wikihouseproject/Skylark/SKYLARK150/Openings/W-O-L-4/W-O-L-4_cnc/W-O-L-4-G.dxf

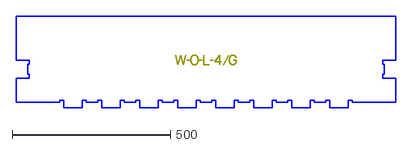
[picture p11: CAD file, 2026-10-01]
SKYLARK150/Openings/W-O-L-4/W-O-L-4_cnc/W-O-L-4-G.dxf
1199.5 x 289.5
