wikihouseproject/Skylark/SKYLARK150/Openings/W-O-L-5/W-O-L-5_cnc/W-O-L-5-B.dxf

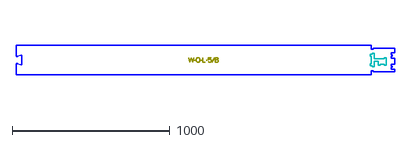
[picture p12: CAD file, 2026-10-01]
SKYLARK150/Openings/W-O-L-5/W-O-L-5_cnc/W-O-L-5-B.dxf
2399.5 x 185.5
