wikihouseproject/Skylark/SKYLARK150/Openings/W-O-M-1/W-O-M-1_cnc/W-O-M-1-I.dxf

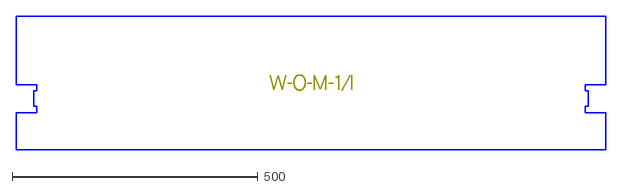
[picture p13: CAD file, 2026-10-01]
SKYLARK150/Openings/W-O-M-1/W-O-M-1_cnc/W-O-M-1-I.dxf
1199.5 x 271.5
