wikihouseproject/Skylark/SKYLARK150/Openings/W-O-M-2/W-O-M-2_cnc/W-O-M-2-B.dxf

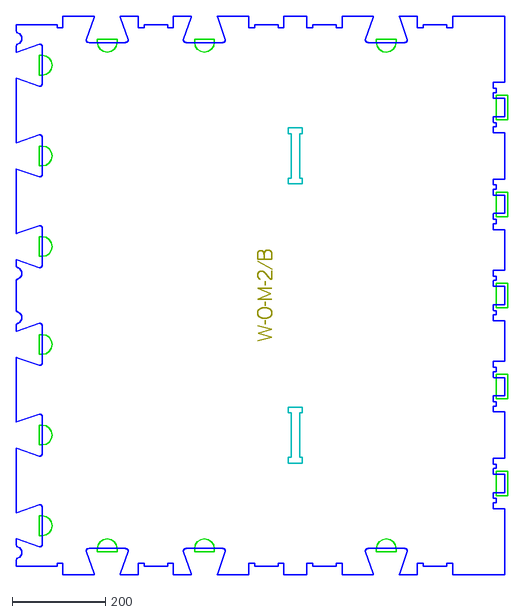
[picture p14: CAD file, 2026-10-01]
SKYLARK150/Openings/W-O-M-2/W-O-M-2_cnc/W-O-M-2-B.dxf
1056.0 x 1199.5
