wikihouseproject/Skylark/SKYLARK150/Openings/W-O-M-3/W-O-M-3_cnc/W-O-M-3-G.dxf

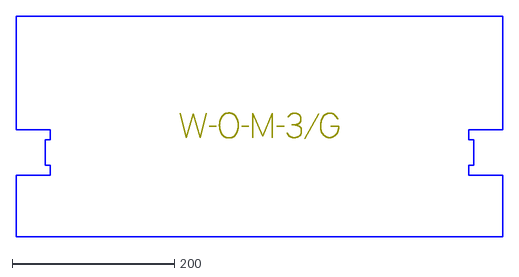
[picture p15: CAD file, 2026-10-01]
SKYLARK150/Openings/W-O-M-3/W-O-M-3_cnc/W-O-M-3-G.dxf
599.5 x 271.5
