wikihouseproject/Skylark/SKYLARK150/Openings/W-O-M-4/W-O-M-4_cnc/W-O-M-4-C.dxf

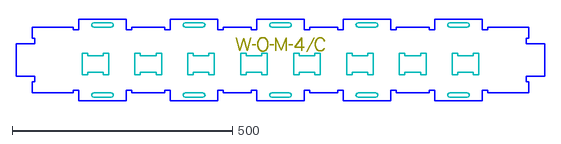
[picture p16: CAD file, 2026-10-01]
SKYLARK150/Openings/W-O-M-4/W-O-M-4_cnc/W-O-M-4-C.dxf
1199.5 x 185.6
