wikihouseproject/Skylark/SKYLARK150/Openings/W-O-M-5/W-O-M-5_cnc/W-O-M-5-C.dxf

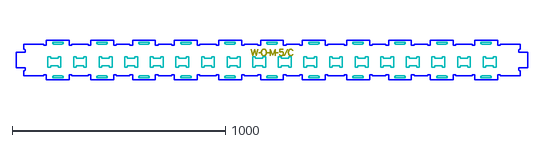
[picture p17: CAD file, 2026-10-01]
SKYLARK150/Openings/W-O-M-5/W-O-M-5_cnc/W-O-M-5-C.dxf
2399.5 x 185.6
