wikihouseproject/Skylark/SKYLARK150/Openings/W-O-S-1/W-O-S-1_cnc/W-O-S-1-H.dxf

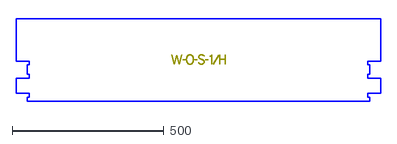
[picture p18: CAD file, 2026-10-01]
SKYLARK150/Openings/W-O-S-1/W-O-S-1_cnc/W-O-S-1-H.dxf
1199.5 x 271.5
