wikihouseproject/Skylark/SKYLARK150/Openings/W-O-S-2/W-O-S-2_cnc/W-O-S-2-B.dxf

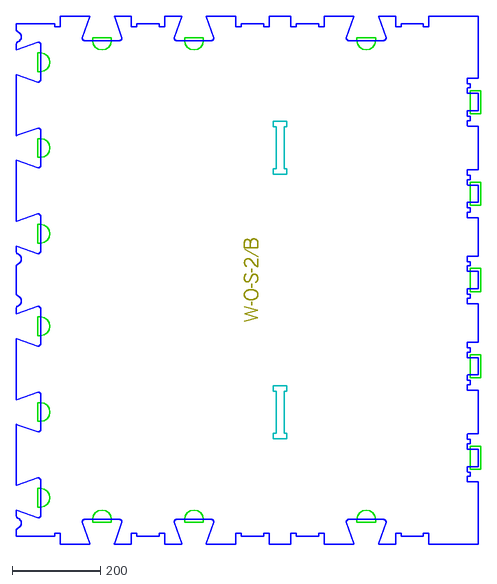
[picture p19: CAD file, 2026-10-01]
SKYLARK150/Openings/W-O-S-2/W-O-S-2_cnc/W-O-S-2-B.dxf
1056.0 x 1199.5
