wikihouseproject/Skylark/SKYLARK150/Openings/W-O-S-3/W-O-S-3_cnc/W-O-S-3-A.dxf

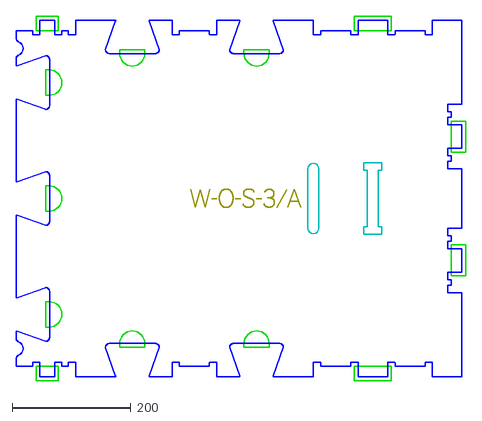
[picture p20: CAD file, 2026-10-01]
SKYLARK150/Openings/W-O-S-3/W-O-S-3_cnc/W-O-S-3-A.dxf
756.0 x 612.5
