wikihouseproject/Skylark/SKYLARK150/Openings/W-O-S-4/W-O-S-4_cnc/W-O-S-4-C.dxf

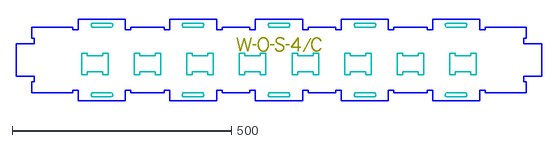
[picture p21: CAD file, 2026-10-01]
SKYLARK150/Openings/W-O-S-4/W-O-S-4_cnc/W-O-S-4-C.dxf
1199.5 x 185.6
