wikihouseproject/Skylark/SKYLARK150/Openings/W-O-S-5/W-O-S-5_cnc/W-O-S-5-A.dxf

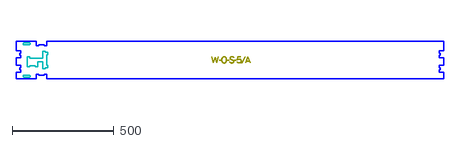
[picture p22: CAD file, 2026-10-01]
SKYLARK150/Openings/W-O-S-5/W-O-S-5_cnc/W-O-S-5-A.dxf
2099.5 x 185.5
