wikihouseproject/Skylark/SKYLARK150/Roofs/R-L-42/R-L-42_cnc/R-L-42-J.dxf

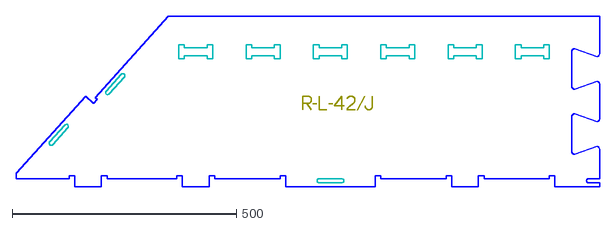
[picture p23: CAD file, 2026-10-01]
SKYLARK150/Roofs/R-L-42/R-L-42_cnc/R-L-42-J.dxf
1299.5 x 379.5
