wikihouseproject/Skylark/SKYLARK150/Roofs/R-L/R-L_cnc/R-L-A.dxf

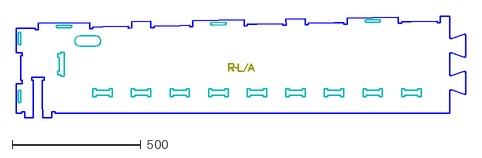
[picture p24: CAD file, 2026-10-01]
SKYLARK150/Roofs/R-L/R-L_cnc/R-L-A.dxf
1747.5 x 394.6
