wikihouseproject/Skylark/SKYLARK150/Roofs/R-S-42/R-S-42_cnc/R-S-42-A.dxf

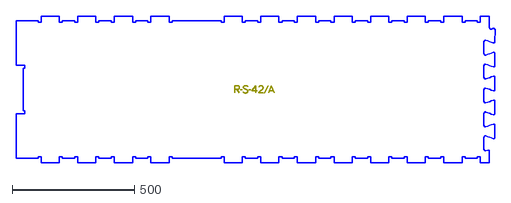
[picture p25: CAD file, 2026-10-01]
SKYLARK150/Roofs/R-S-42/R-S-42_cnc/R-S-42-A.dxf
1962.6 x 599.5
