wikihouseproject/Skylark/SKYLARK150/Roofs/R-S/R-S_cnc/R-S-L.dxf

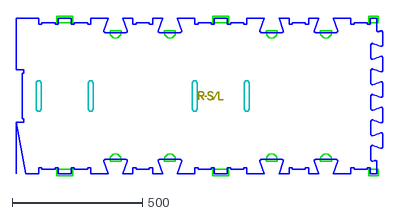
[picture p26: CAD file, 2026-10-01]
SKYLARK150/Roofs/R-S/R-S_cnc/R-S-L.dxf
1408.5 x 612.5
