wikihouseproject/Skylark/SKYLARK150/Roofs/R-XXS-42/R-XXS-42_cnc/R-XXS-42-A.dxf

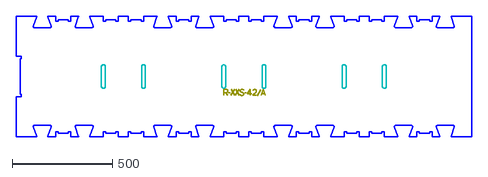
[picture p27: CAD file, 2026-10-01]
SKYLARK150/Roofs/R-XXS-42/R-XXS-42_cnc/R-XXS-42-A.dxf
2268.2 x 599.5
