wikihouseproject/Skylark/SKYLARK150/Roofs/R-XXS/R-XXS_cnc/R-XXS-J.dxf

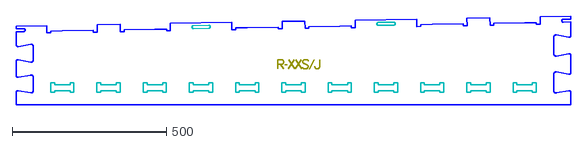
[picture p28: CAD file, 2026-10-01]
SKYLARK150/Roofs/R-XXS/R-XXS_cnc/R-XXS-J.dxf
1799.5 x 286.0
