wikihouseproject/Skylark/SKYLARK150/Walls/C-L-1/C-L-1_cnc/C-L-1-H.dxf

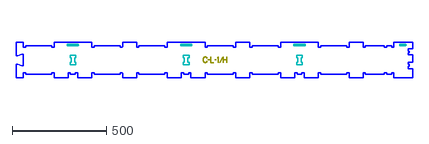
[picture p29: CAD file, 2026-10-01]
SKYLARK150/Walls/C-L-1/C-L-1_cnc/C-L-1-H.dxf
2099.5 x 185.5
