wikihouseproject/Skylark/SKYLARK150/Walls/C-L-2/C-L-2_cnc/C-L-2-E.dxf

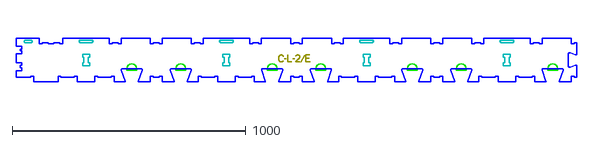
[picture p30: CAD file, 2026-10-01]
SKYLARK150/Walls/C-L-2/C-L-2_cnc/C-L-2-E.dxf
2399.5 x 185.5
