wikihouseproject/Skylark/SKYLARK150/Walls/C-M-1/C-M-1_cnc/C-M-1-C.dxf

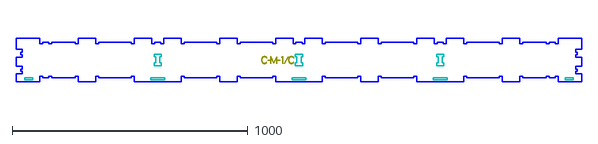
[picture p31: CAD file, 2026-10-01]
SKYLARK150/Walls/C-M-1/C-M-1_cnc/C-M-1-C.dxf
2399.5 x 185.5
