wikihouseproject/Skylark/SKYLARK150/Walls/C-M-2/C-M-2_cnc/C-M-2-E.dxf

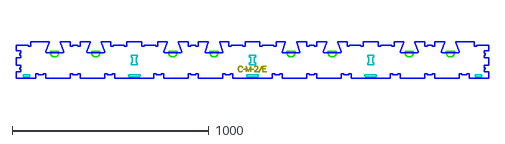
[picture p32: CAD file, 2026-10-01]
SKYLARK150/Walls/C-M-2/C-M-2_cnc/C-M-2-E.dxf
2399.5 x 185.5
