wikihouseproject/Skylark/SKYLARK150/Walls/C-S-1/C-S-1_cnc/C-S-1-B.dxf

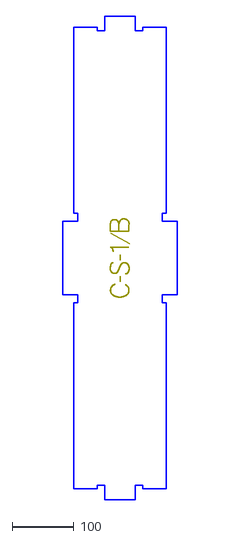
[picture p33: CAD file, 2026-10-01]
SKYLARK150/Walls/C-S-1/C-S-1_cnc/C-S-1-B.dxf
185.5 x 785.5
