wikihouseproject/Skylark/SKYLARK150/Walls/C-S-2/C-S-2_cnc/C-S-2-D.dxf

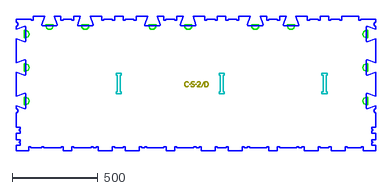
[picture p34: CAD file, 2026-10-01]
SKYLARK150/Walls/C-S-2/C-S-2_cnc/C-S-2-D.dxf
2099.5 x 785.5
