wikihouseproject/Skylark/SKYLARK150/Walls/G-S-42-1/G-S-42-1_cnc/G-S-42-1-A.dxf

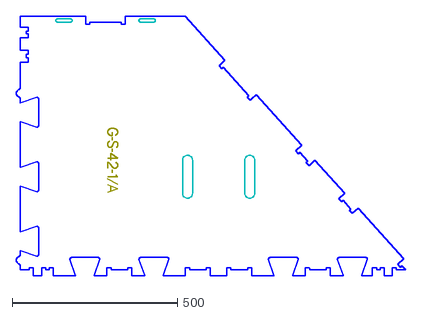
[picture p35: CAD file, 2026-10-01]
SKYLARK150/Walls/G-S-42-1/G-S-42-1_cnc/G-S-42-1-A.dxf
1177.3 x 785.5
