wikihouseproject/Skylark/SKYLARK150/Walls/G-S-42-2/G-S-42-2_cnc/G-S-42-2-E.dxf

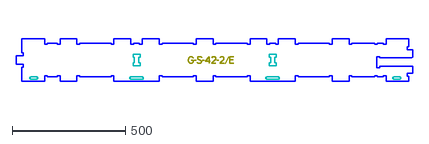
[picture p36: CAD file, 2026-10-01]
SKYLARK150/Walls/G-S-42-2/G-S-42-2_cnc/G-S-42-2-E.dxf
1748.2 x 185.5
