wikihouseproject/Skylark/SKYLARK150/Walls/G-S-42-3/G-S-42-3_cnc/G-S-42-3-E.dxf

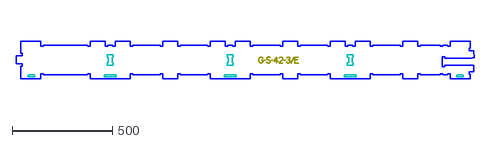
[picture p37: CAD file, 2026-10-01]
SKYLARK150/Walls/G-S-42-3/G-S-42-3_cnc/G-S-42-3-E.dxf
2288.4 x 185.5
