wikihouseproject/Skylark/SKYLARK150/Walls/G-S-42-4/G-S-42-4_cnc/G-S-42-4-A.dxf

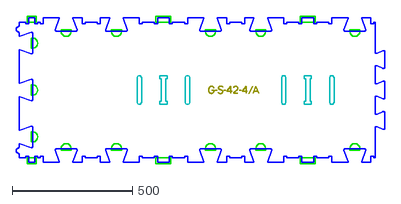
[picture p38: CAD file, 2026-10-01]
SKYLARK150/Walls/G-S-42-4/G-S-42-4_cnc/G-S-42-4-A.dxf
1531.5 x 612.5
