wikihouseproject/Skylark/SKYLARK150/Walls/G-S-42-4R/G-S-42-4R_cnc/G-S-42-4R-C.dxf

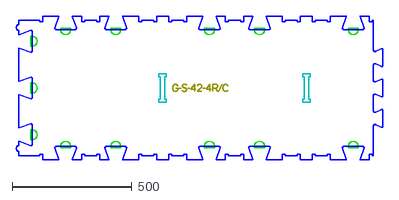
[picture p39: CAD file, 2026-10-01]
SKYLARK150/Walls/G-S-42-4R/G-S-42-4R_cnc/G-S-42-4R-C.dxf
1531.5 x 599.5
