wikihouseproject/Skylark/SKYLARK150/Walls/G-S-42-5R/G-S-42-5R_cnc/G-S-42-5R-C.dxf

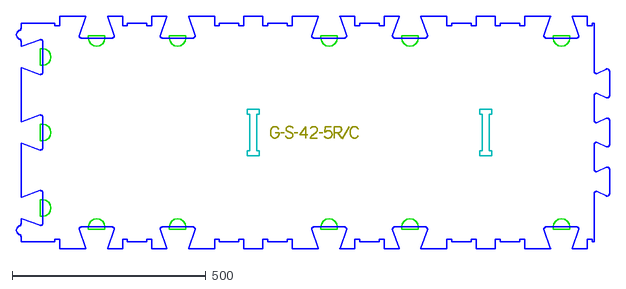
[picture p40: CAD file, 2026-10-01]
SKYLARK150/Walls/G-S-42-5R/G-S-42-5R_cnc/G-S-42-5R-C.dxf
1531.5 x 599.5
