wikihouseproject/Skylark/SKYLARK150/Walls/G-S-42-6/G-S-42-6_cnc/G-S-42-6-C.dxf

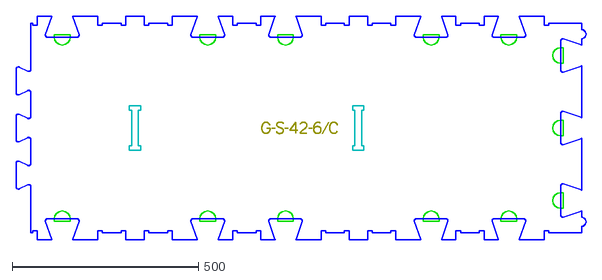
[picture p41: CAD file, 2026-10-01]
SKYLARK150/Walls/G-S-42-6/G-S-42-6_cnc/G-S-42-6-C.dxf
1531.5 x 599.5
