wikihouseproject/Skylark/SKYLARK150/Walls/G-S-42-7/G-S-42-7_cnc/G-S-42-7-C.dxf

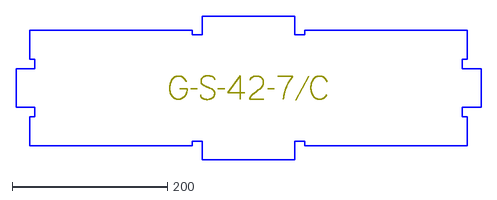
[picture p42: CAD file, 2026-10-01]
SKYLARK150/Walls/G-S-42-7/G-S-42-7_cnc/G-S-42-7-C.dxf
599.5 x 185.5
