wikihouseproject/Skylark/SKYLARK150/Walls/G-S-42-8/G-S-42-8_cnc/G-S-42-8-D.dxf

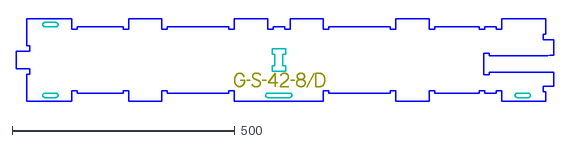
[picture p43: CAD file, 2026-10-01]
SKYLARK150/Walls/G-S-42-8/G-S-42-8_cnc/G-S-42-8-D.dxf
1207.9 x 185.5
