wikihouseproject/Skylark/SKYLARK150/Walls/G-S-42-9/G-S-42-9_cnc/G-S-42-9-E.dxf

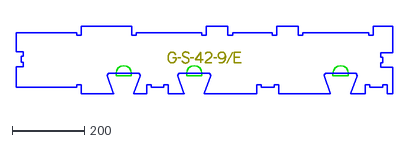
[picture p44: CAD file, 2026-10-01]
SKYLARK150/Walls/G-S-42-9/G-S-42-9_cnc/G-S-42-9-E.dxf
1042.2 x 185.5
