wikihouseproject/Skylark/SKYLARK150/Walls/G-XXS-42-1/G-XXS-42-1_cnc/G-XXS-42-1-E.dxf

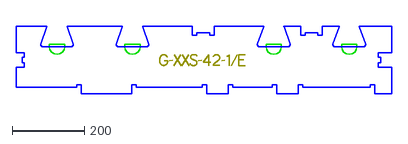
[picture p45: CAD file, 2026-10-01]
SKYLARK150/Walls/G-XXS-42-1/G-XXS-42-1_cnc/G-XXS-42-1-E.dxf
1039.1 x 185.5
