wikihouseproject/Skylark/SKYLARK150/Walls/G-XXS-42-2/G-XXS-42-2_cnc/G-XXS-42-2-F.dxf

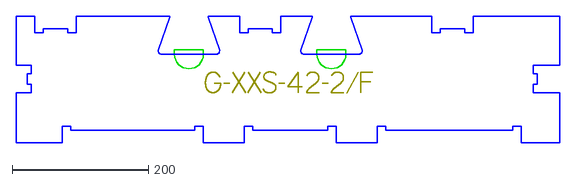
[picture p46: CAD file, 2026-10-01]
SKYLARK150/Walls/G-XXS-42-2/G-XXS-42-2_cnc/G-XXS-42-2-F.dxf
796.5 x 185.5
