wikihouseproject/Skylark/SKYLARK150/Walls/G-XXS-42-3R/G-XXS-42-3R_cnc/G-XXS-42-3R-E.dxf

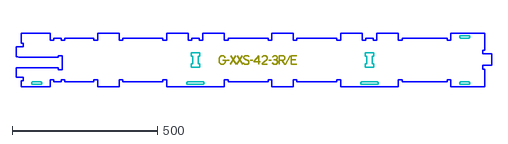
[picture p47: CAD file, 2026-10-01]
SKYLARK150/Walls/G-XXS-42-3R/G-XXS-42-3R_cnc/G-XXS-42-3R-E.dxf
1639.2 x 185.5
