wikihouseproject/Skylark/SKYLARK150/Walls/G-XXS-42-4/G-XXS-42-4_cnc/G-XXS-42-4-D.dxf

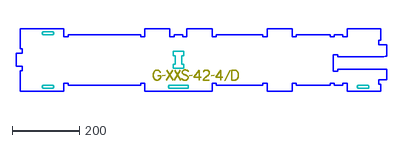
[picture p48: CAD file, 2026-10-01]
SKYLARK150/Walls/G-XXS-42-4/G-XXS-42-4_cnc/G-XXS-42-4-D.dxf
1098.8 x 185.5
