wikihouseproject/Skylark/SKYLARK150/Walls/G-XXS-42-5/G-XXS-42-5_cnc/G-XXS-42-5-B.dxf

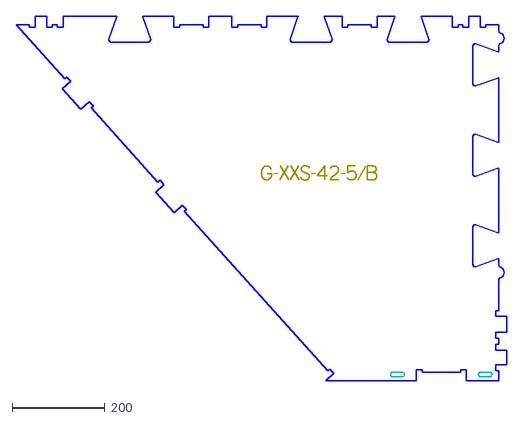
[picture p49: CAD file, 2026-10-01]
SKYLARK150/Walls/G-XXS-42-5/G-XXS-42-5_cnc/G-XXS-42-5-B.dxf
1058.3 x 785.6
