wikihouseproject/Skylark/SKYLARK150/Walls/V-L-1/V-L-1_cnc/V-L-1-K.dxf

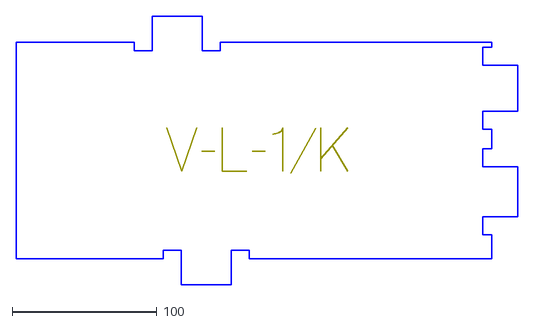
[picture p50: CAD file, 2026-10-01]
SKYLARK150/Walls/V-L-1/V-L-1_cnc/V-L-1-K.dxf
346.3 x 185.5
