wikihouseproject/Skylark/SKYLARK150/Walls/V-L-2/V-L-2_cnc/V-L-2-H.dxf

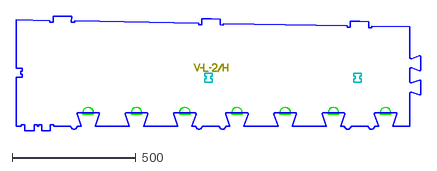
[picture p51: CAD file, 2026-10-01]
SKYLARK150/Walls/V-L-2/V-L-2_cnc/V-L-2-H.dxf
1633.4 x 463.0
