wikihouseproject/Skylark/SKYLARK150/Walls/V-S-1/V-S-1_cnc/V-S-1-A.dxf

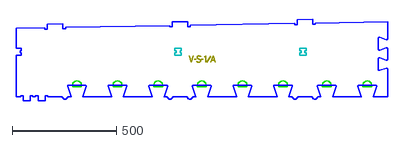
[picture p52: CAD file, 2026-10-01]
SKYLARK150/Walls/V-S-1/V-S-1_cnc/V-S-1-A.dxf
1782.9 x 389.7
