wikihouseproject/Skylark/SKYLARK150/Walls/V-S-2/V-S-2_cnc/V-S-2-J.dxf

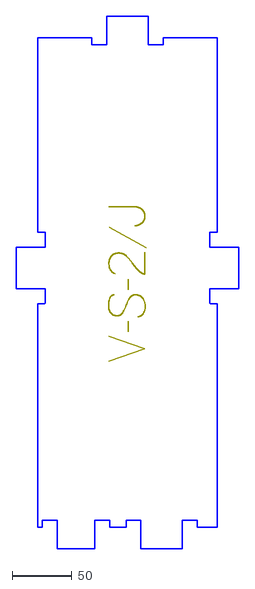
[picture p53: CAD file, 2026-10-01]
SKYLARK150/Walls/V-S-2/V-S-2_cnc/V-S-2-J.dxf
185.5 x 445.0
