wikihouseproject/Skylark/SKYLARK150/Walls/V-XXS-1/V-XXS-1_cnc/V-XXS-1-F.dxf

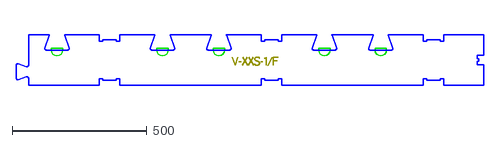
[picture p54: CAD file, 2026-10-01]
SKYLARK150/Walls/V-XXS-1/V-XXS-1_cnc/V-XXS-1-F.dxf
1731.4 x 185.5
