wikihouseproject/Skylark/SKYLARK150/Walls/V-XXS-2/V-XXS-2_cnc/V-XXS-2-E.dxf

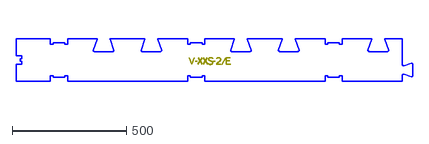
[picture p55: CAD file, 2026-10-01]
SKYLARK150/Walls/V-XXS-2/V-XXS-2_cnc/V-XXS-2-E.dxf
1731.4 x 185.5
