wikihouseproject/Skylark/SKYLARK150/Walls/W-L/W-L_cnc/W-L-B.dxf

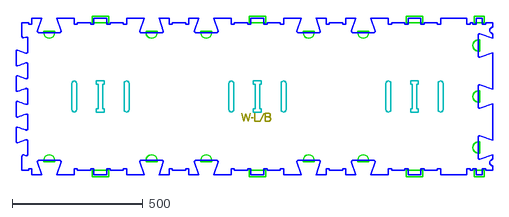
[picture p56: CAD file, 2026-10-01]
SKYLARK150/Walls/W-L/W-L_cnc/W-L-B.dxf
1822.1 x 612.5
