wikihouseproject/Skylark/SKYLARK150/Walls/W-M/W-M_cnc/W-M-C.dxf

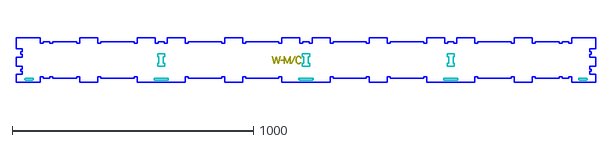
[picture p57: CAD file, 2026-10-01]
SKYLARK150/Walls/W-M/W-M_cnc/W-M-C.dxf
2399.5 x 185.5
