wikihouseproject/Skylark/SKYLARK150/Walls/W-S/W-S_cnc/W-S-A.dxf

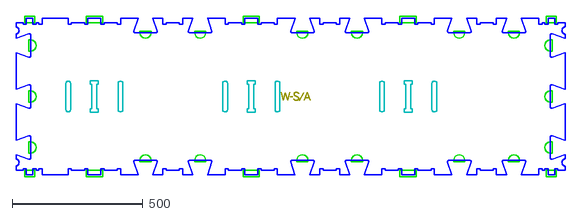
[picture p58: CAD file, 2026-10-01]
SKYLARK150/Walls/W-S/W-S_cnc/W-S-A.dxf
2099.5 x 612.5
