wikihouseproject/Skylark/SKYLARK200/Other/SKYLARK200_COMB-F_END-Y2/SKYLARK200_COMB-F_END-Y1.dxf

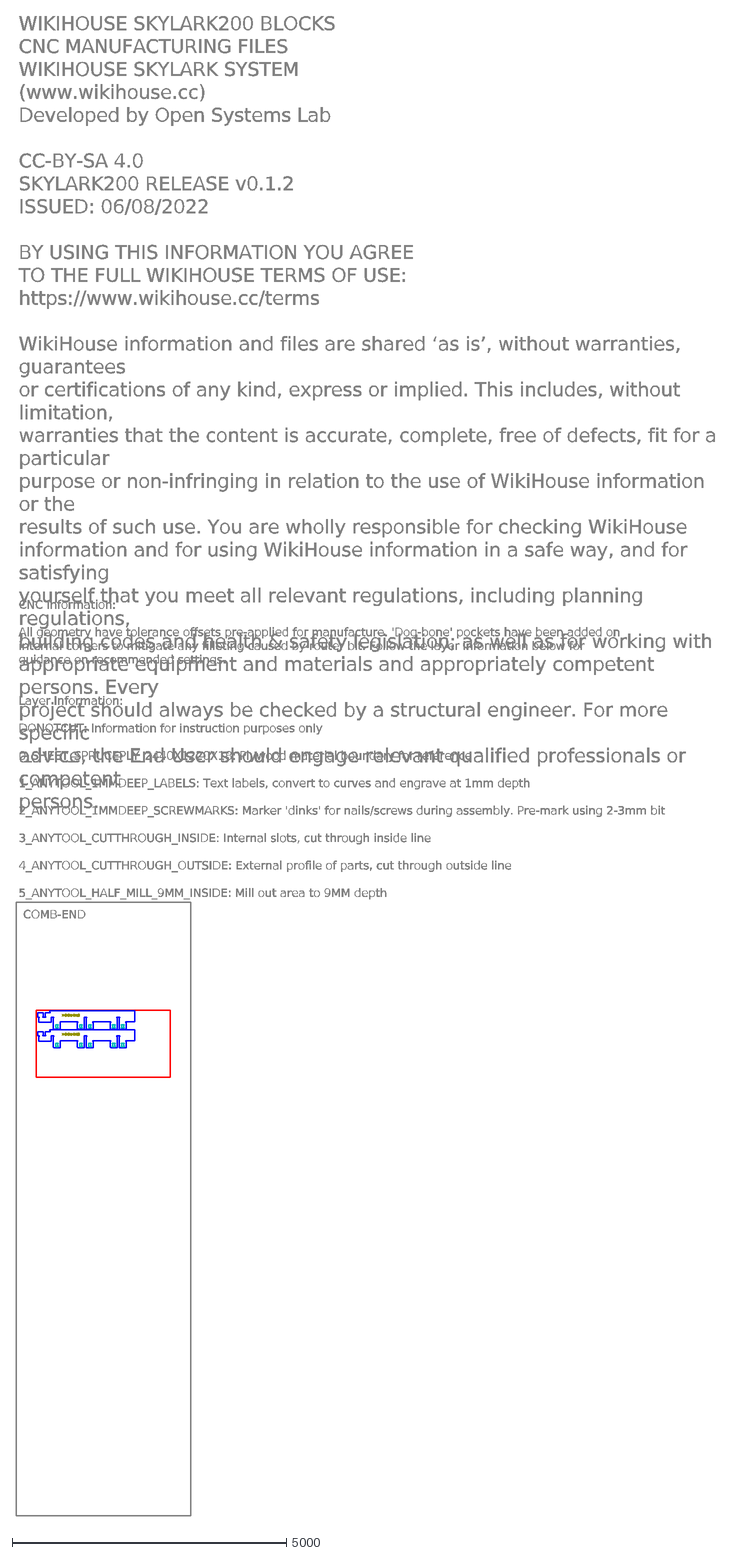
[picture p59: CAD file, 2022-09-02]
SKYLARK200/Other/SKYLARK200_COMB-F_END-Y2/SKYLARK200_COMB-F_END-Y1.dxf
WIKIHOUSE SKYLARK200 BLOCKS CNC MANUFACTURING FILES WIKIHOUSE SKYLARK SYSTEM (www.wikihouse.cc) Developed by Open Systems Lab CC-BY-SA 4.0 SKYLARK200 RELEASE v0
CNC Information: All geometry have tolerance offsets pre-applied for manufacture. 'Dog-bone' pockets have been added on internal corners to mitigate any filleti
COMB-END
