wikihouseproject/Skylark/SKYLARK200/Roofs/SKYLARK200_ROOF-42-XXS/SKYLARK200_ROOF-42-XXS_cnc.dxf

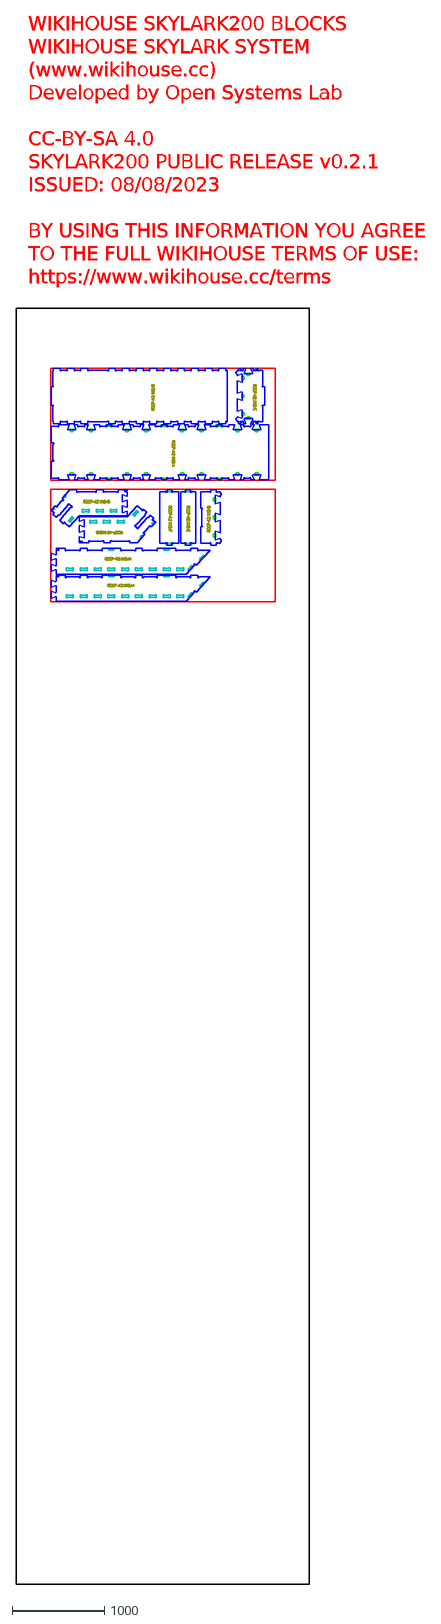
[picture p60: CAD file, 2023-08-10]
SKYLARK200/Roofs/SKYLARK200_ROOF-42-XXS/SKYLARK200_ROOF-42-XXS_cnc.dxf
WIKIHOUSE SKYLARK200 BLOCKS WIKIHOUSE SKYLARK SYSTEM (www.wikihouse.cc) Developed by Open Systems Lab CC-BY-SA 4.0 SKYLARK200 PUBLIC RELEASE v0.2.1 ISSUED: 08/0
